Sardau/Sardauscan/STL/DSC_0300.jpg

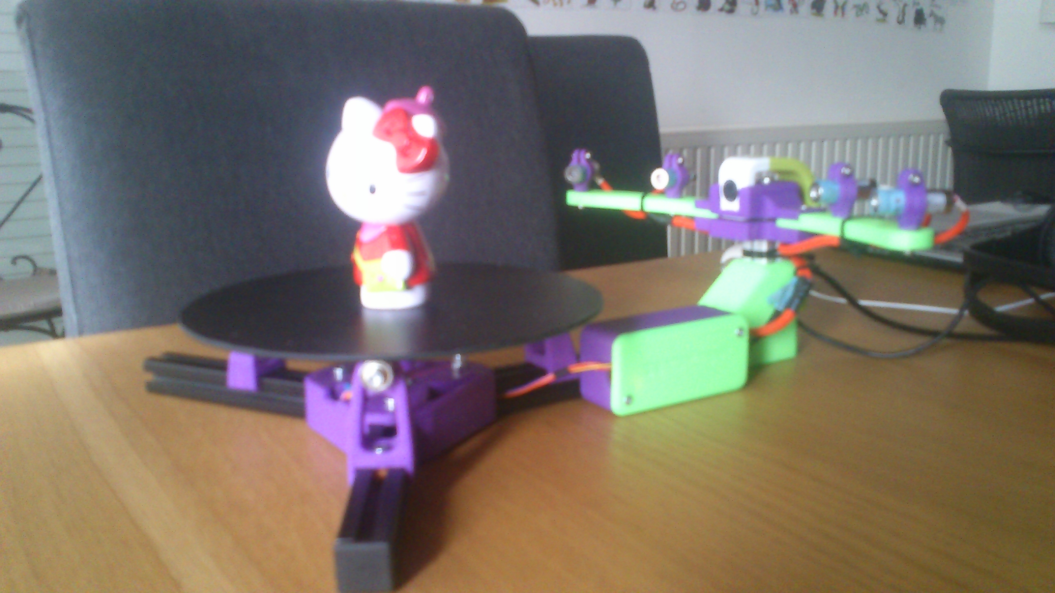
STL/DSC_0300.jpg
