Sardau/Sardauscan/STL/DSC_0301.jpg

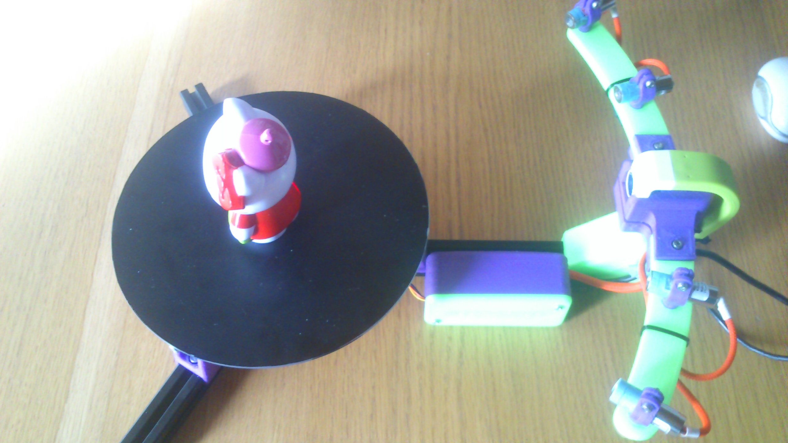
STL/DSC_0301.jpg
