Sardau/Sardauscan/STL/DSC_0302.jpg

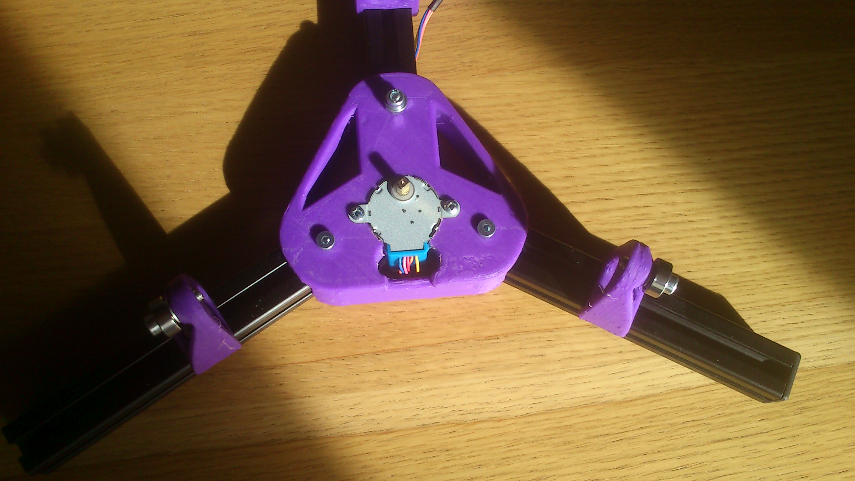
STL/DSC_0302.jpg
