Sardau/Sardauscan/STL/DSC_0303.jpg

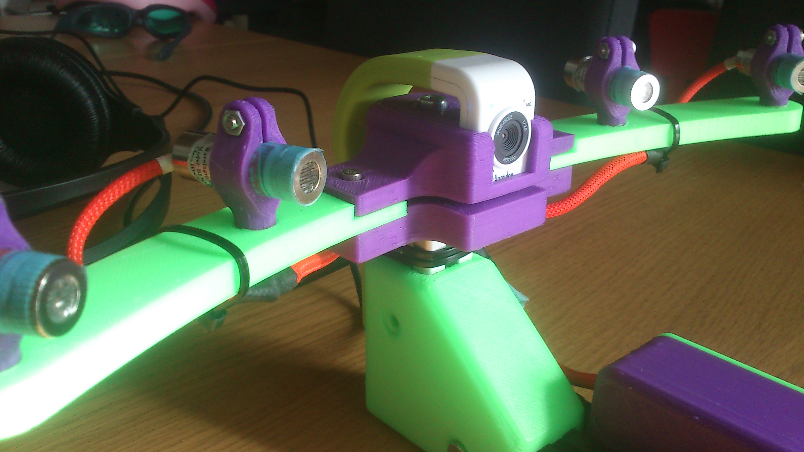
STL/DSC_0303.jpg
