Sardau/Sardauscan/STL/DSC_0304.jpg

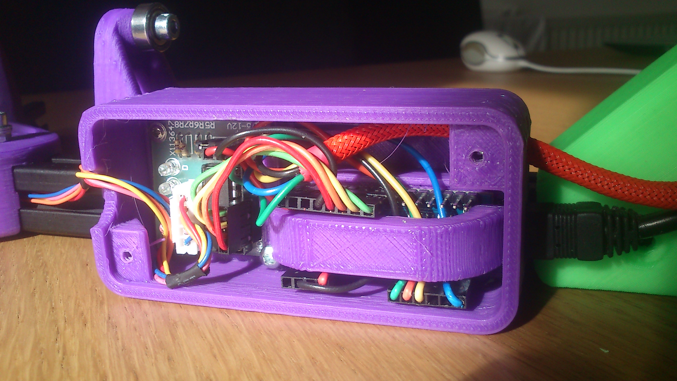
STL/DSC_0304.jpg
