Sardau/Sardauscan/STL/DSC_0305.jpg

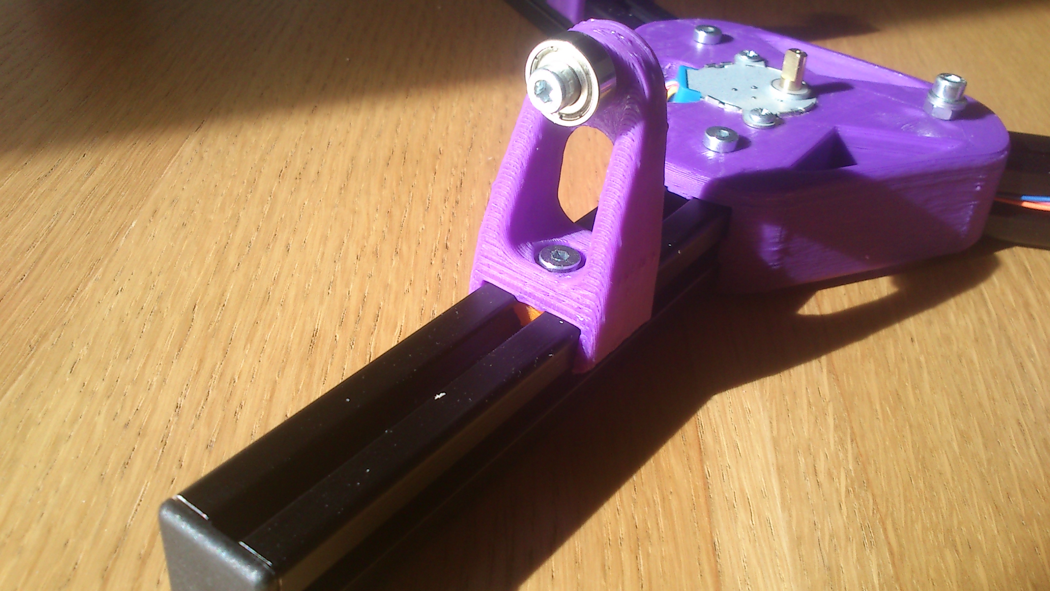
STL/DSC_0305.jpg
